technobly/VEXTREME/code/stm32/fatfs/doc/img/modules.png

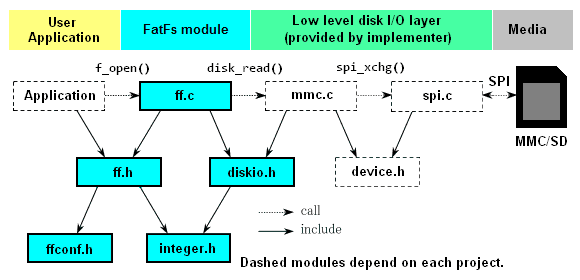
code/stm32/fatfs/doc/img/modules.png
