technobly/VEXTREME/hall-of-fame/01 - Brett Walach - v0.1/v0.1-bot.jpg

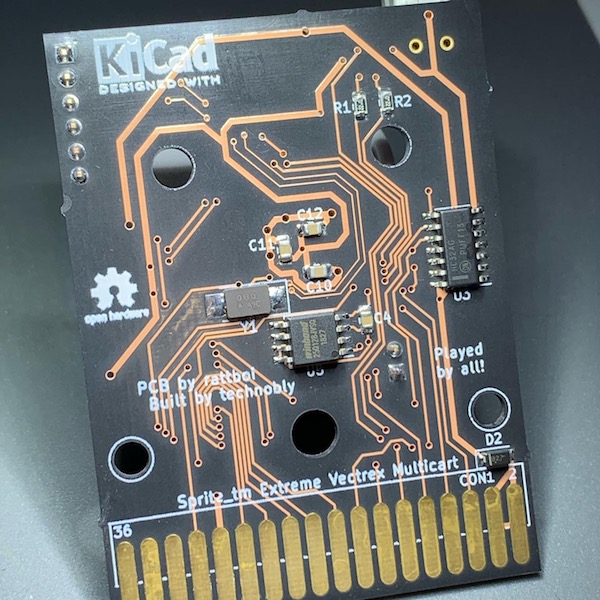
hall-of-fame/01 - Brett Walach - v0.1/v0.1-bot.jpg
