technobly/VEXTREME/hall-of-fame/02 - Mike Danick - v0.1/v0.1-menu.jpg

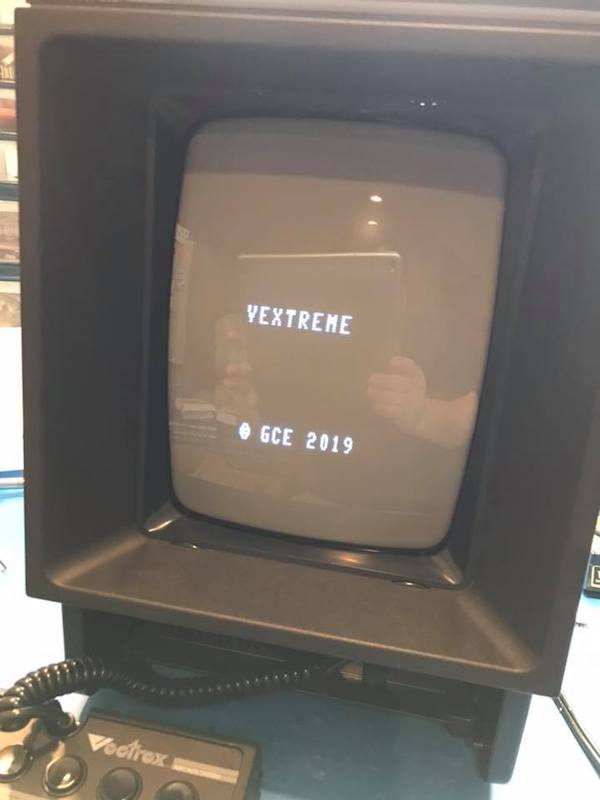
hall-of-fame/02 - Mike Danick - v0.1/v0.1-menu.jpg
