technobly/VEXTREME/hall-of-fame/09 - Bill MacDonald - v0.2/v0.2 - bot.png

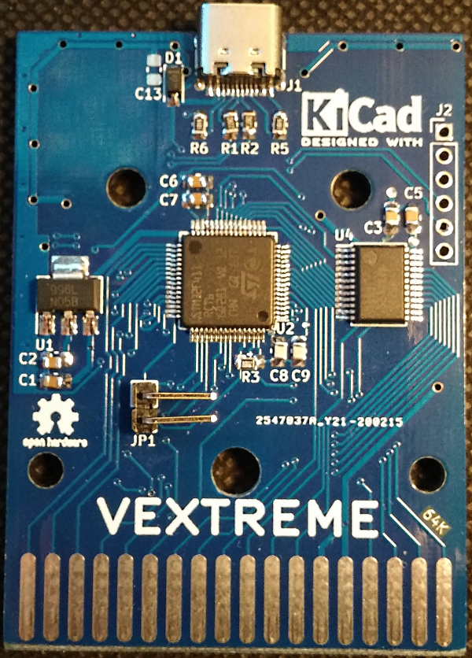
hall-of-fame/09 - Bill MacDonald - v0.2/v0.2 - bot.png
