technobly/VEXTREME/hall-of-fame/09 - Bill MacDonald - v0.2/v0.2 - top.png

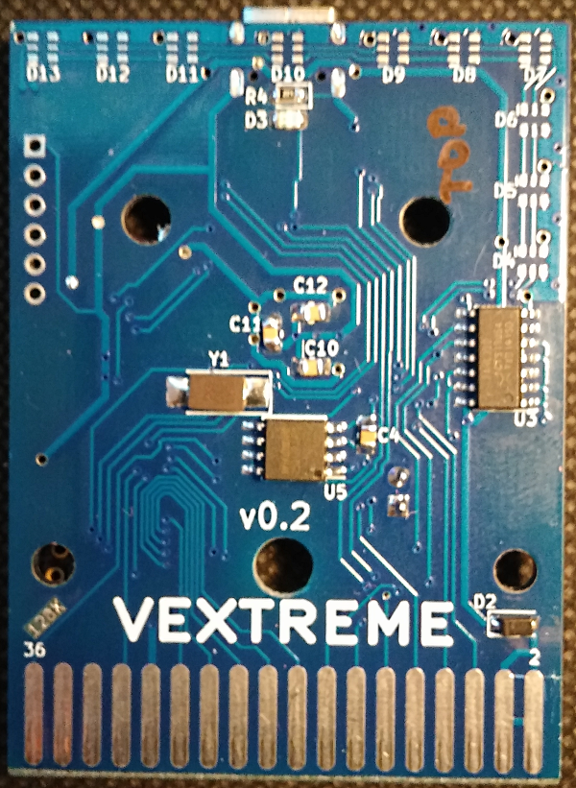
hall-of-fame/09 - Bill MacDonald - v0.2/v0.2 - top.png
