technobly/VEXTREME/hall-of-fame/11 - Andrej Gerbec - v0.2/v0.2 - leds.jpg

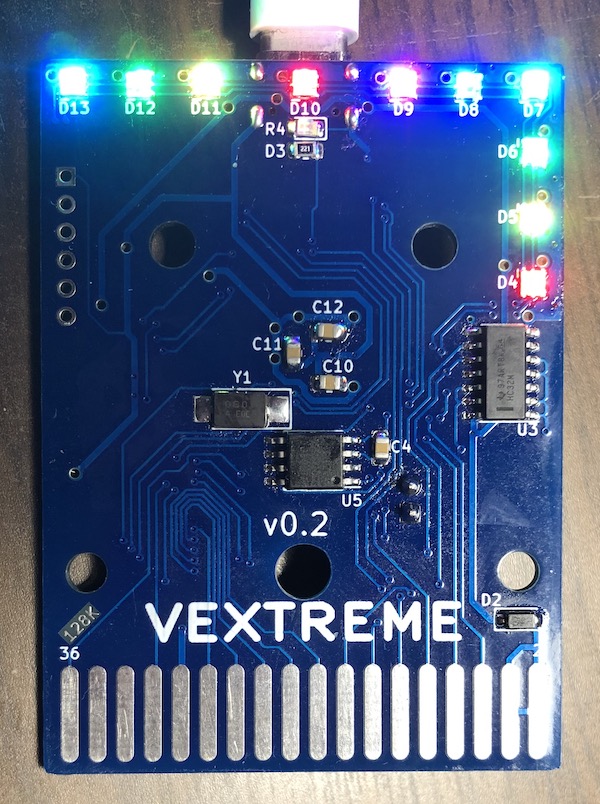
hall-of-fame/11 - Andrej Gerbec - v0.2/v0.2 - leds.jpg
