technobly/VEXTREME/hall-of-fame/12 - Viandou64 - v0.2/v0.2 - case.jpg

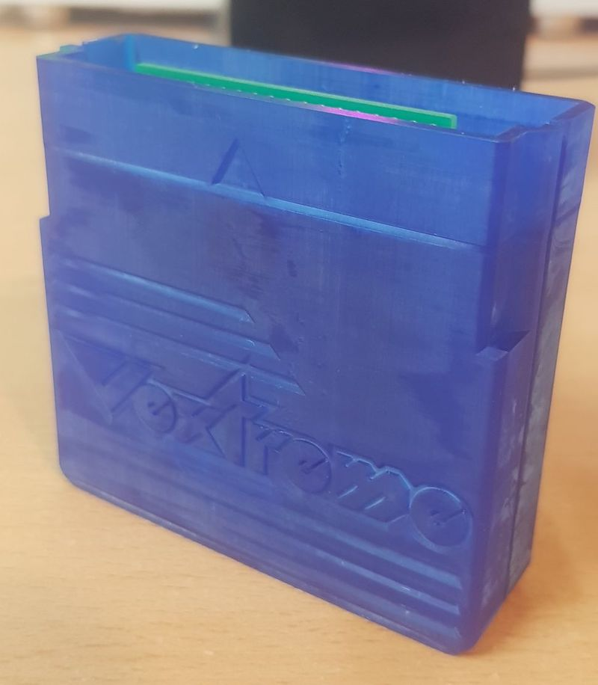
hall-of-fame/12 - Viandou64 - v0.2/v0.2 - case.jpg
