technobly/VEXTREME/hall-of-fame/13 - Marcel Prisi - v0.2/v0.2 - bootscreen.jpg

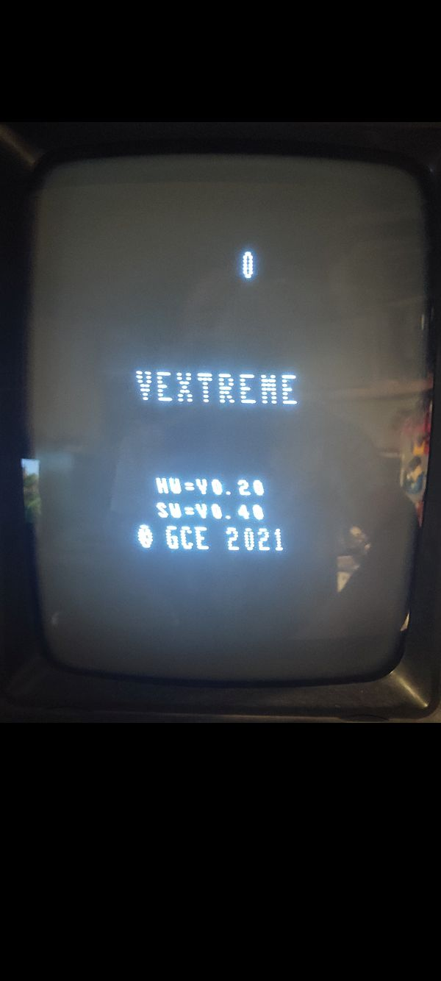
hall-of-fame/13 - Marcel Prisi - v0.2/v0.2 - bootscreen.jpg
