technobly/VEXTREME/hall-of-fame/13 - Marcel Prisi - v0.2/v0.2 - lightson.jpg

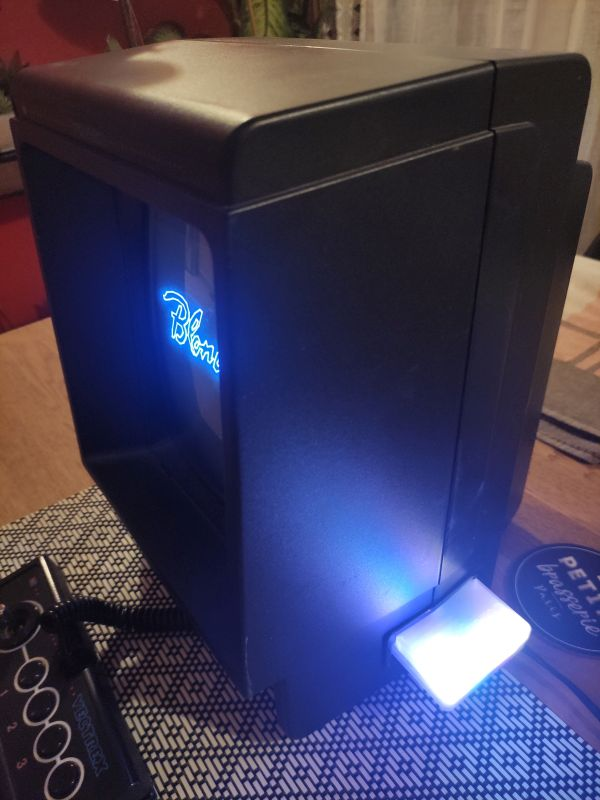
hall-of-fame/13 - Marcel Prisi - v0.2/v0.2 - lightson.jpg
