technobly/VEXTREME/hall-of-fame/13 - Marcel Prisi - v0.2/v0.2 - menu.jpg

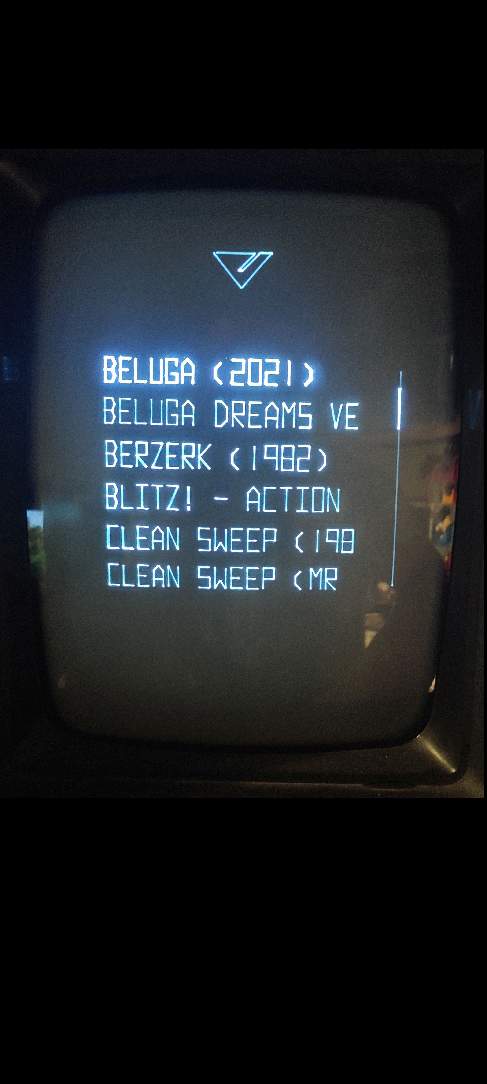
hall-of-fame/13 - Marcel Prisi - v0.2/v0.2 - menu.jpg
