technobly/VEXTREME/hall-of-fame/13 - Marcel Prisi - v0.2/v0.2 - top.jpg

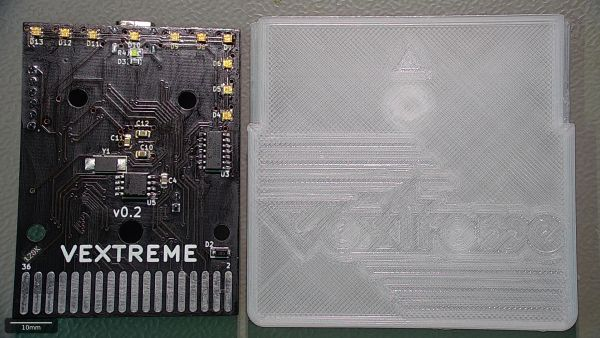
hall-of-fame/13 - Marcel Prisi - v0.2/v0.2 - top.jpg
